Blazer2020/RoboCraft/Images/IMG-20250602-WA0008.jpg

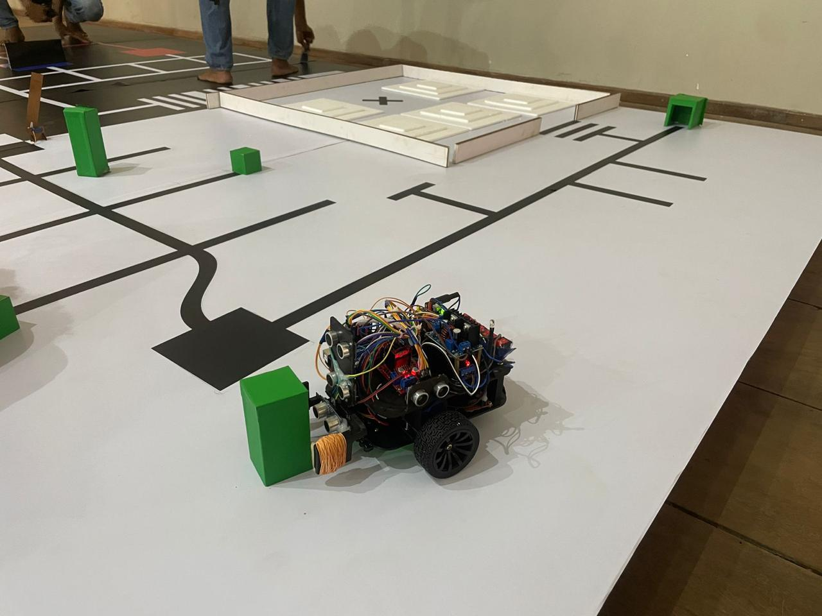
Images/IMG-20250602-WA0008.jpg
